LightNeO/esp-32-internet-radio/images/2.jpg

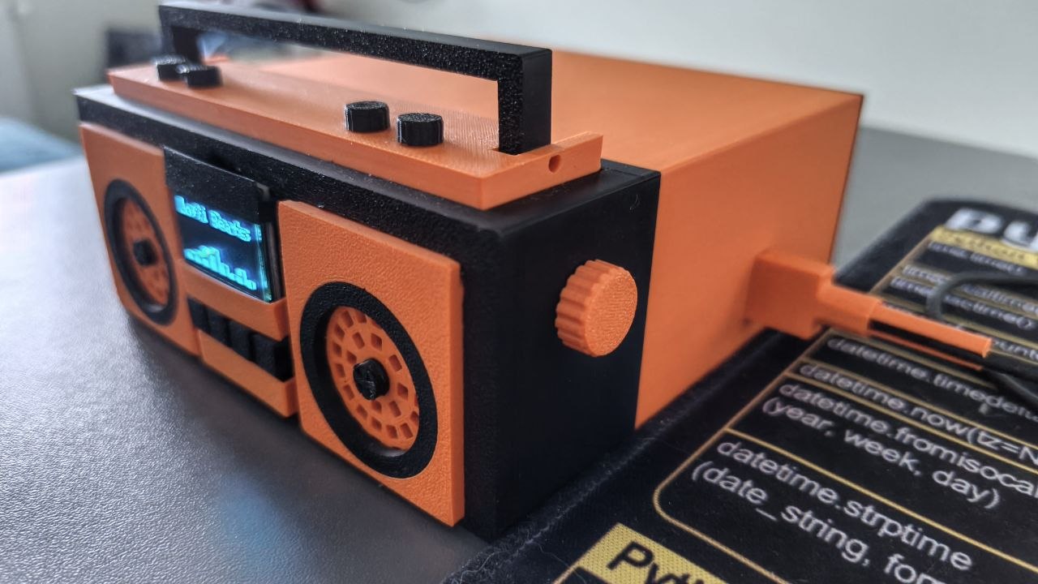
images/2.jpg
